jctots/telegram-doorman/kicad/telegram-doorman.kicad_sch

## KiCad design kicad/telegram-doorman.kicad_sch (2024-06-28, an earlier design)

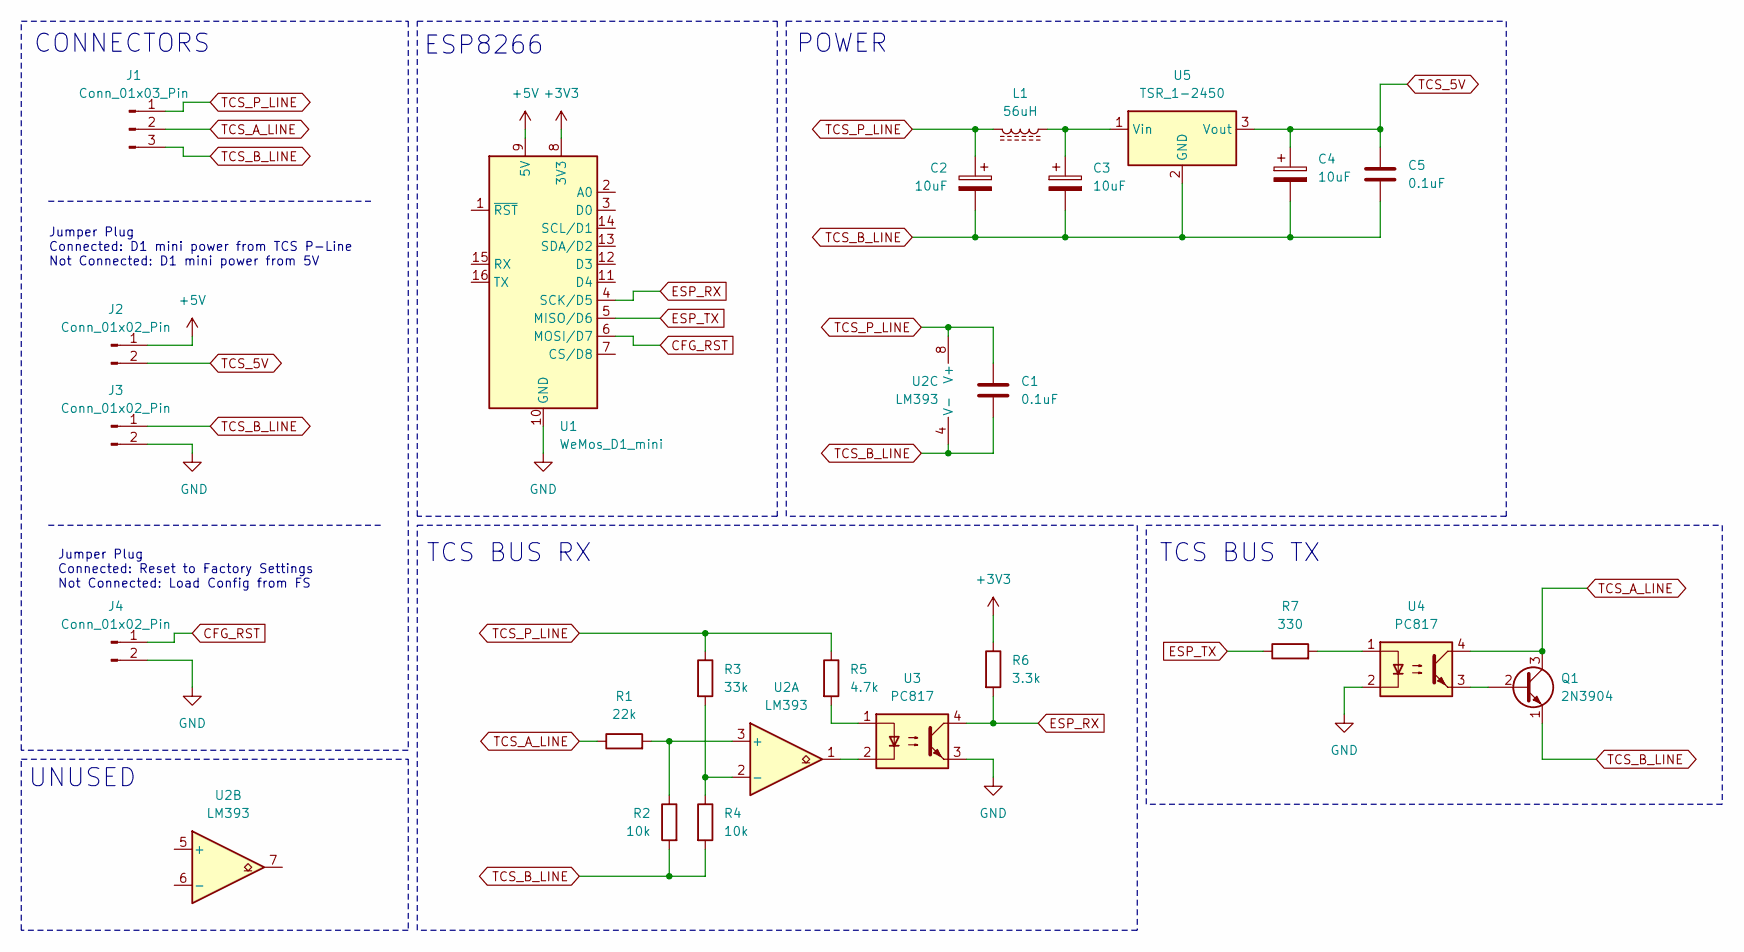
[picture p11: schematic telegram-doorman.kicad_sch]

Parts:
C1, C5: 0.1uF
C2, C3, C4: 10uF
J1: Conn_01x03_Pin
J2, J3, J4: Conn_01x02_Pin
L1: 56uH
Q1: 2N3904; TO-92_Inline
R1: 22k
R2, R4: 10k
R3: 33k
R5: 4.7k
R6: 3.3k
R7: 330
U1: WeMos_D1_mini; WEMOS_D1_mini_light
U2: LM393
U3, U4: PC817; DIP-4_W7.62mm
U5: TSR_1-2450; Converter_DCDC_TRACO_TSR-1_THT

Connections:
+3V3: R6.1, U1.8 (3V3)
+5V: J2.1, U1.9 (5V)
CFG_RST: J4.1, U1.6 (MOSI/D7)
ESP_RX: R6.2, U1.4 (SCK/D5), U3.4
ESP_TX: R7.1, U1.5 (MISO/D6)
GND: J3.2, J4.2, U1.10 (GND), U3.3, U4.2
unnamed: C3.1, L1.1, U5.1 (Vin)
unnamed: Q1.2 (B), U4.3
unnamed: R1.2, R2.1, U2.3 (+)
unnamed: R3.2, R4.1, U2.2 (-)
unnamed: R5.2, U3.1
unnamed: R7.2, U4.1
unnamed: U2.1, U3.2
TCS_5V: C4.1, C5.1, J2.2, U5.3 (Vout)
TCS_A_LINE: J1.2, Q1.3 (C), R1.1, U4.4
TCS_B_LINE: C1.2, C2.2, C3.2, C4.2, C5.2, J1.3, J3.1, Q1.1 (E), R2.2, R4.2, U2.4 (V-), U5.2 (GND)
TCS_P_LINE: C1.1, C2.1, J1.1, L1.2, R3.1, R5.1, U2.8 (V+)

Notes on the sheet:
TCS BUS TX
UNUSED
TCS BUS RX
Jumper Plug Connected: Reset to Factory Settings Not Connected: Load Config from FS
ESP8266
Jumper Plug Connected: D1 mini power from TCS P-Line Not Connected: D1 mini power from 5V
POWER
CONNECTORS
